Global-Health-Engineering/h2s-monitor/media/video/README.md

# Videos

Video recordings of the device in operation.
